kak-tus/compressor/compressor.kicad_pcb

## KiCad design GORAT circuit diagram/GORAT circuit diagram.kicad_pcb

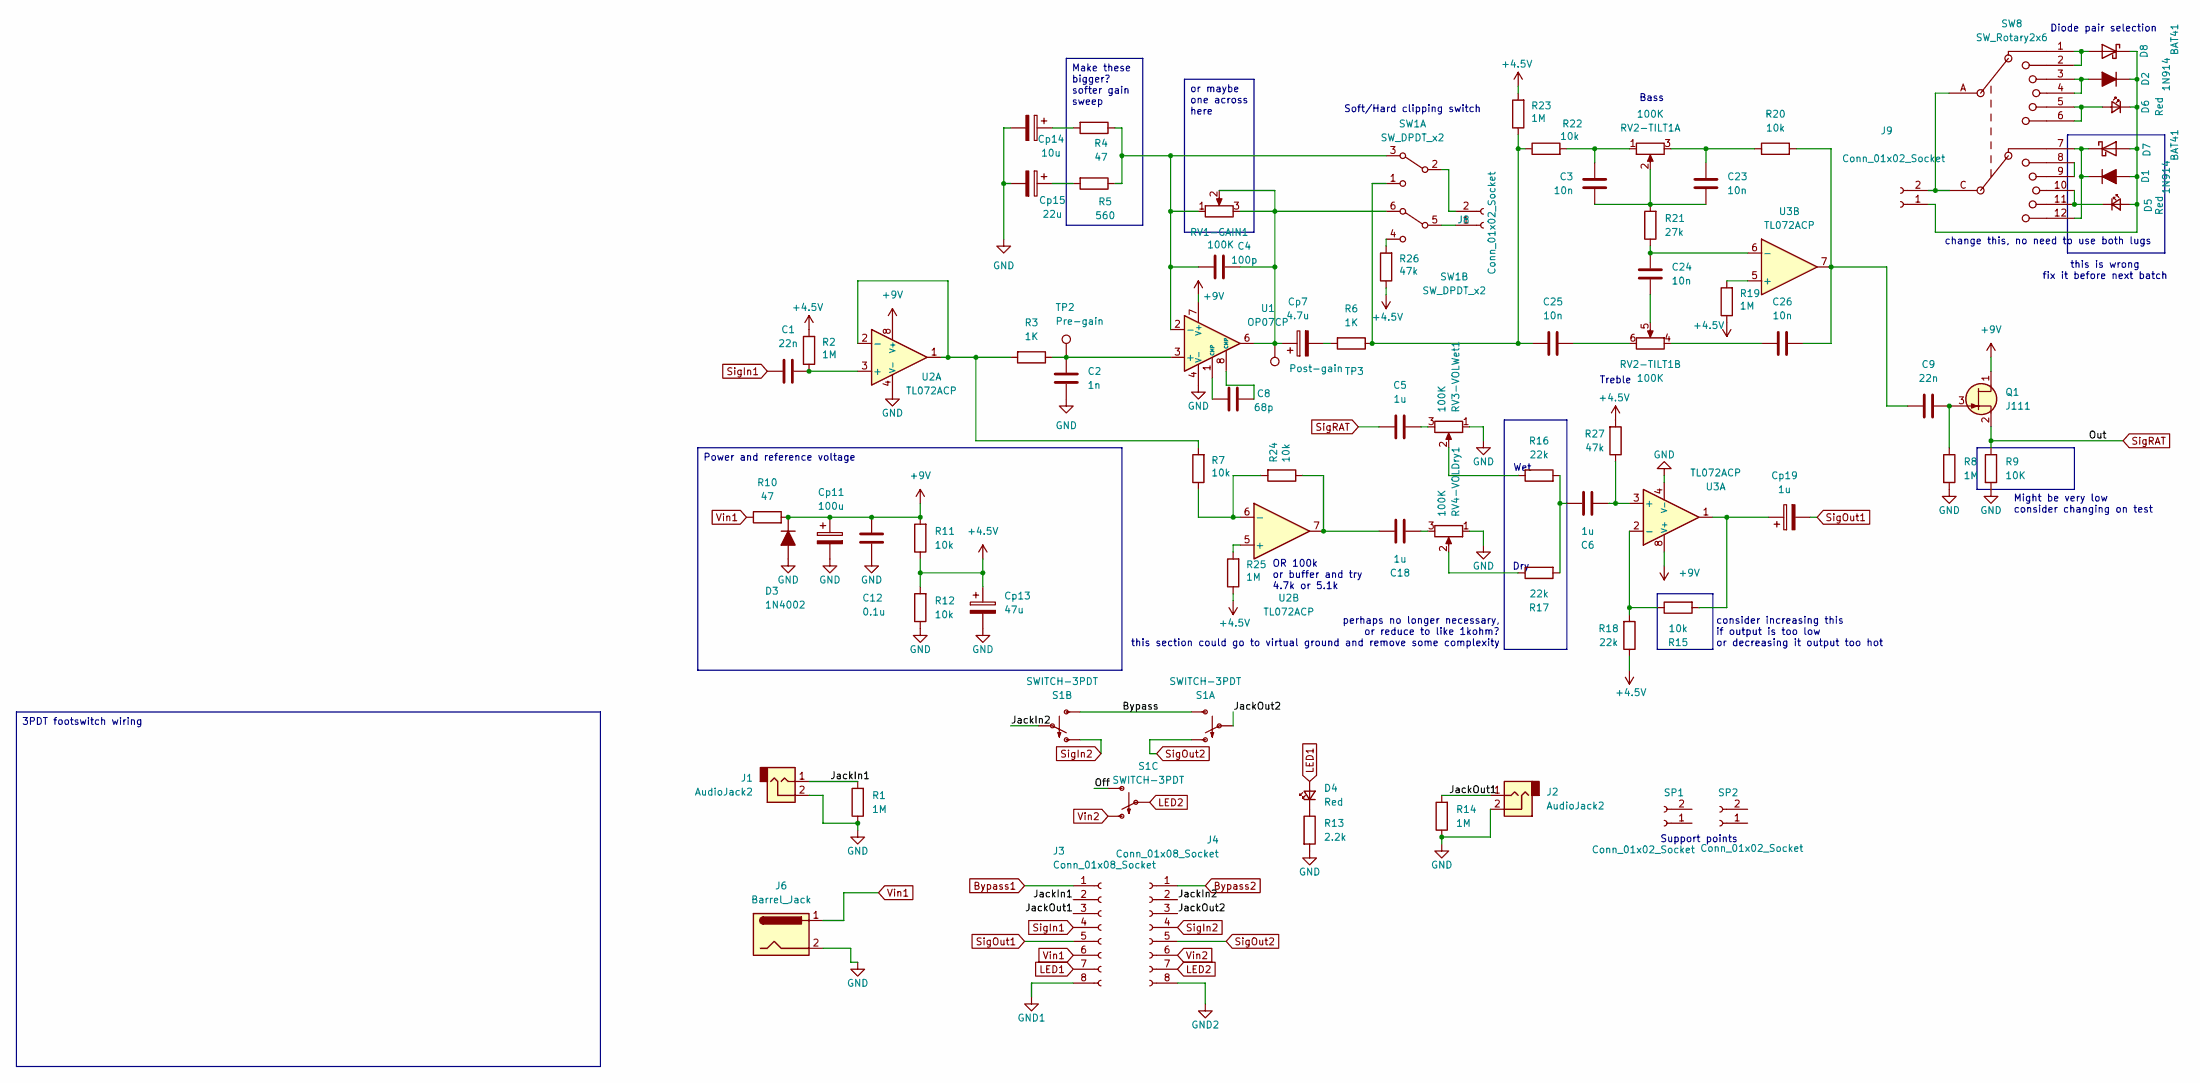
[picture p3: schematic GORAT circuit diagram.kicad_sch]

Parts:
C1, C9: 22n; C_Disc_D4.7mm_W2.5mm_P5.00mm
C2: 1n; C_Disc_D4.7mm_W2.5mm_P5.00mm
C3, C23, C24, C25, C26: 10n; C_Disc_D4.7mm_W2.5mm_P5.00mm
C4: 100p; C_Disc_D4.7mm_W2.5mm_P5.00mm
C5, C6, C18: 1u; C_Disc_D4.7mm_W2.5mm_P5.00mm
C8: 68p; C_Disc_D4.7mm_W2.5mm_P5.00mm
C12: 0.1u; C_Disc_D4.7mm_W2.5mm_P5.00mm
Cp7: 4.7u; CP_Radial_D5.0mm_P2.50mm
Cp11: 100u; CP_Radial_D5.0mm_P2.50mm
Cp13: 47u; CP_Radial_D5.0mm_P2.50mm
Cp14: 10u; CP_Radial_D5.0mm_P2.50mm
Cp15: 22u; CP_Radial_D5.0mm_P2.50mm
Cp19: 1u; CP_Radial_D5.0mm_P2.50mm
D1, D2: 1N914; D_DO-35_SOD27_P7.62mm_Horizontal
D3: 1N4002; D_DO-41_SOD81_P7.62mm_Horizontal
D4: Red; LED_D5.0mm
D5, D6: Red; LED_D3.0mm
D7, D8: BAT41; D_DO-35_SOD27_P7.62mm_Horizontal
J1, J2: AudioJack2; SolderWire-0.75sqmm_1x02_P7mm_D1.25mm_OD3.5mm
J3, J4: Conn_01x08_Socket; PinHeader_1x08_P2.54mm_Vertical
J6: Barrel_Jack; SolderWire-0.5sqmm_1x02_P4.6mm_D0.9mm_OD2.1mm
J8, J9: Conn_01x02_Socket; PinHeader_1x02_P2.54mm_Vertical
Q1: J111; TO-92_Inline_Wide_DSG
R1, R2, R8, R14, R19, R23, R25: 1M; R_Axial_DIN0207_L6.3mm_D2.5mm_P10.16mm_Horizontal
R3, R6: 1K; R_Axial_DIN0207_L6.3mm_D2.5mm_P10.16mm_Horizontal
R4, R10: 47; R_Axial_DIN0207_L6.3mm_D2.5mm_P10.16mm_Horizontal
R5: 560; R_Axial_DIN0207_L6.3mm_D2.5mm_P10.16mm_Horizontal
R7, R11, R12, R15, R20, R22, R24: 10k; R_Axial_DIN0207_L6.3mm_D2.5mm_P10.16mm_Horizontal
R9: 10K; R_Axial_DIN0207_L6.3mm_D2.5mm_P10.16mm_Horizontal
R13: 2.2k; R_Axial_DIN0207_L6.3mm_D2.5mm_P10.16mm_Horizontal
R16, R17, R18: 22k; R_Axial_DIN0207_L6.3mm_D2.5mm_P10.16mm_Horizontal
R21: 27k; R_Axial_DIN0207_L6.3mm_D2.5mm_P10.16mm_Horizontal
R26, R27: 47k; R_Axial_DIN0207_L6.3mm_D2.5mm_P10.16mm_Horizontal
RV1-GAIN1, RV3-VOLWet1, RV4-VOLDry1: 100K; Potentiometer_Alpha_RD901F-40-00D_Single_Vertical
RV2-TILT1: 100K; Potentiometer_Alpha_RD902F-40-00D_Dual_Vertical
S1: SWITCH-3PDT; 3PDT_fixed
SP1, SP2: Conn_01x02_Socket; PinHeader_1x02_P2.54mm_Vertical
SW1: SW_DPDT_x2; DPDT_fixed
SW8: SW_Rotary2x6; RS26
TP2: Pre-gain; TestPoint_Pad_D2.0mm
TP3: Post-gain; TestPoint_Pad_D2.0mm
U1: OP07CP; DIP-8_W7.62mm_LongPads
U2, U3: TL072ACP; DIP-8_W7.62mm_LongPads

Connections:
+4.5V: Cp13.1, R2.2, R11.1, R12.2, R18.1, R19.1, R23.2, R25.1, R26.1, R27.2
+9V: C12.2, Cp11.1, D3.1 (K), Q1.1 (D), R10.2, R11.2, U1.7 (V+), U2.8 (V+), U3.8 (V+)
/Bypass: S1.P$3 (S), S1.P$6 (S)
/JackIn1: J1.1, J3.2, R1.2
/JackIn2: J4.2, S1.P$5
/JackOut1: J2.1, J3.3, R14.2
/JackOut2: J4.3, S1.P$2
/Off: S1.P$9 (S)
Bypass1: J3.1
Bypass2: J4.1
GND: C2.1, C12.1, Cp11.2, Cp13.2, Cp14.2, Cp15.2, D3.2 (A), J1.2, J2.2, J6.2, R1.1, R8.2, R9.2, R12.1, R13.2, R14.1, RV3-VOLWet1.1, RV4-VOLDry1.1, U1.4 (V-), U2.4 (V-), U3.4 (V-)
GND1: J3.8
GND2: J4.8
LED1: D4.2 (A), J3.7
LED2: J4.7, S1.P$8
unnamed: C3.2, R22.2, RV2-TILT1.1
unnamed: C5.2, RV3-VOLWet1.3
unnamed: C6.1, R16.2, R17.2
unnamed: C8.1, U1.1 (CMP)
unnamed: C8.2, U1.8 (CMP)
unnamed: C18.1, R24.1, U2.7
unnamed: C18.2, RV4-VOLDry1.3
unnamed: C3.1, C23.1, R21.2, RV2-TILT1.2
unnamed: C23.2, R20.1, RV2-TILT1.3
unnamed: C24.1, RV2-TILT1.5
unnamed: C25.1, RV2-TILT1.6
unnamed: C9.2, C26.1, R20.2, U3.7
unnamed: C26.2, RV2-TILT1.4
unnamed: Cp7.2, R6.2
unnamed: Cp14.1, R4.2
unnamed: Cp15.1, R5.2
unnamed: Cp19.1, R15.2, U3.1
unnamed: D1.2 (A), D2.1 (K), D5.2 (A), D6.1 (K), D7.2 (A), D8.1 (K), J9.1
unnamed: D1.1 (K), D7.1 (K), SW8.7, SW8.12
unnamed: D2.2 (A), SW8.3, SW8.4
unnamed: D4.1 (K), R13.1
unnamed: D5.1 (K), SW8.10, SW8.11
unnamed: D6.2 (A), SW8.5, SW8.6
unnamed: D8.2 (A), SW8.1, SW8.2
unnamed: J8.1, SW1.5 (B)
unnamed: J8.2, SW1.2 (B)
unnamed: J9.2, SW8.A, SW8.C
unnamed: C9.1, Q1.3 (G), R8.1
unnamed: R16.1, RV3-VOLWet1.2
unnamed: R17.1, RV4-VOLDry1.2
unnamed: C25.2, R6.1, R22.1, R23.1, SW1.1 (A)
unnamed: C4.2, R4.1, R5.1, RV1-GAIN1.1, SW1.3 (C), U1.2 (-)
unnamed: R26.2, SW1.4 (A)
unnamed: C4.1, Cp7.1, RV1-GAIN1.2, RV1-GAIN1.3, SW1.6 (C), TP3.1, U1.6
unnamed: SW8.8, SW8.9
unnamed: C2.2, R3.1, TP2.1, U1.3 (+)
unnamed: C1.2, R2.1, U2.3 (+)
unnamed: R3.2, R7.2, U2.1, U2.2 (-)
unnamed: R25.2, U2.5 (+)
unnamed: R7.1, R24.2, U2.6 (-)
unnamed: C6.2, R27.1, U3.3 (+)
unnamed: R15.1, R18.2, U3.2 (-)
unnamed: R19.2, U3.5 (+)
unnamed: C24.2, R21.1, U3.6 (-)
SigIn1: C1.1, J3.4
SigIn2: J4.4, S1.P$4 (O)
SigOut1: Cp19.2, J3.5
SigOut2: J4.5, S1.P$1 (O)
SigRAT: C5.1, Q1.2 (S), R9.1
Vin1: J3.6, J6.1, R10.1
Vin2: J4.6, S1.P$7 (O)

Notes on the sheet:
Wet
OR 100k or buffer and try 4.7k or 5.1k
Might be very low consider changing on test
Soft/Hard clipping switch
consider increasing this if output is too low or decreasing it output too hot
change this, no need to use both lugs
Treble
Support points
Bass
perhaps no longer necessary, or reduce to like 1kohm? this section could go to virtual ground and remove some complexity
Diode pair selection
Dry
this is wrong fix it before next batch
or maybe one across here
Make these bigger? softer gain sweep
3PDT footswitch wiring
Power and reference voltage

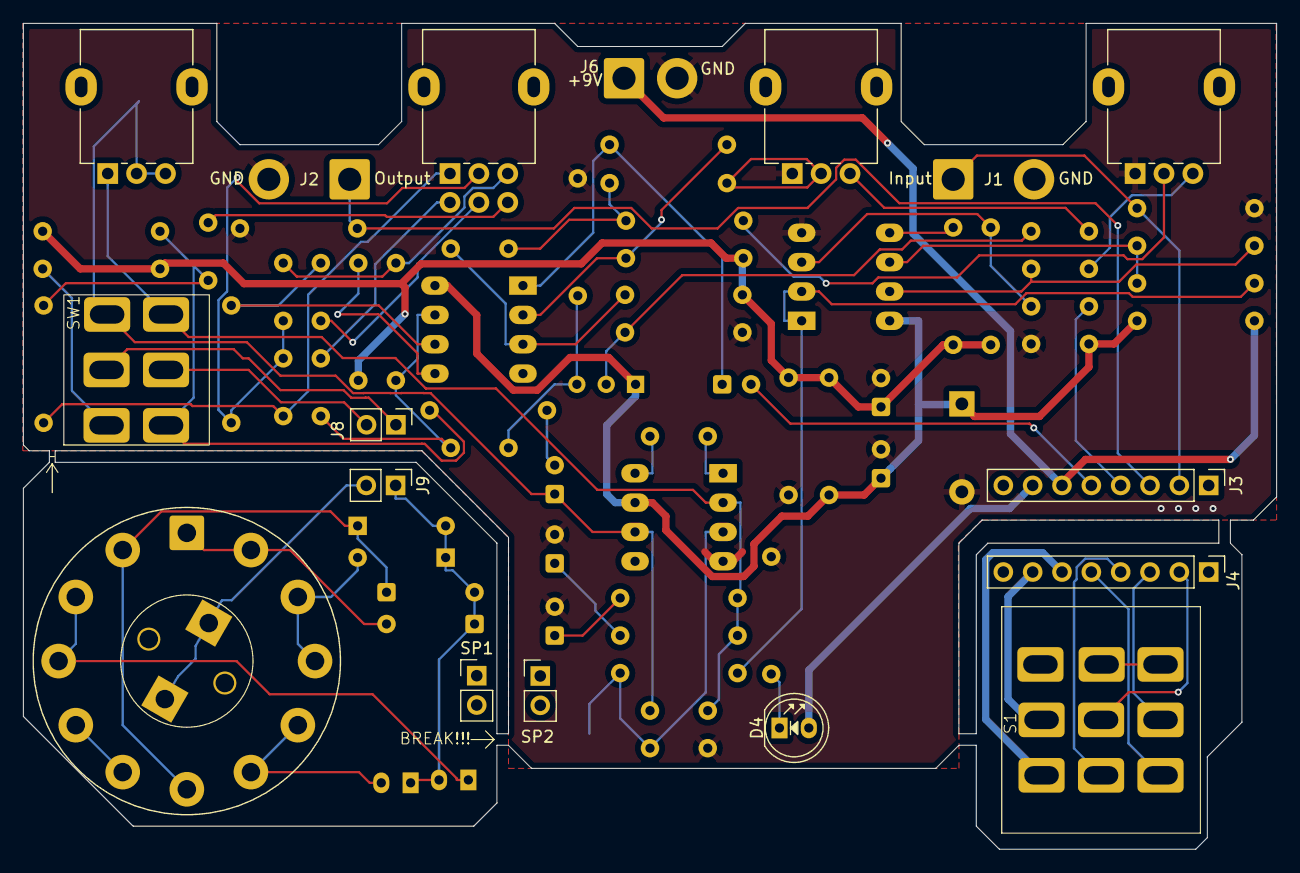
[picture p4: board GORAT circuit diagram.kicad_pcb from above]

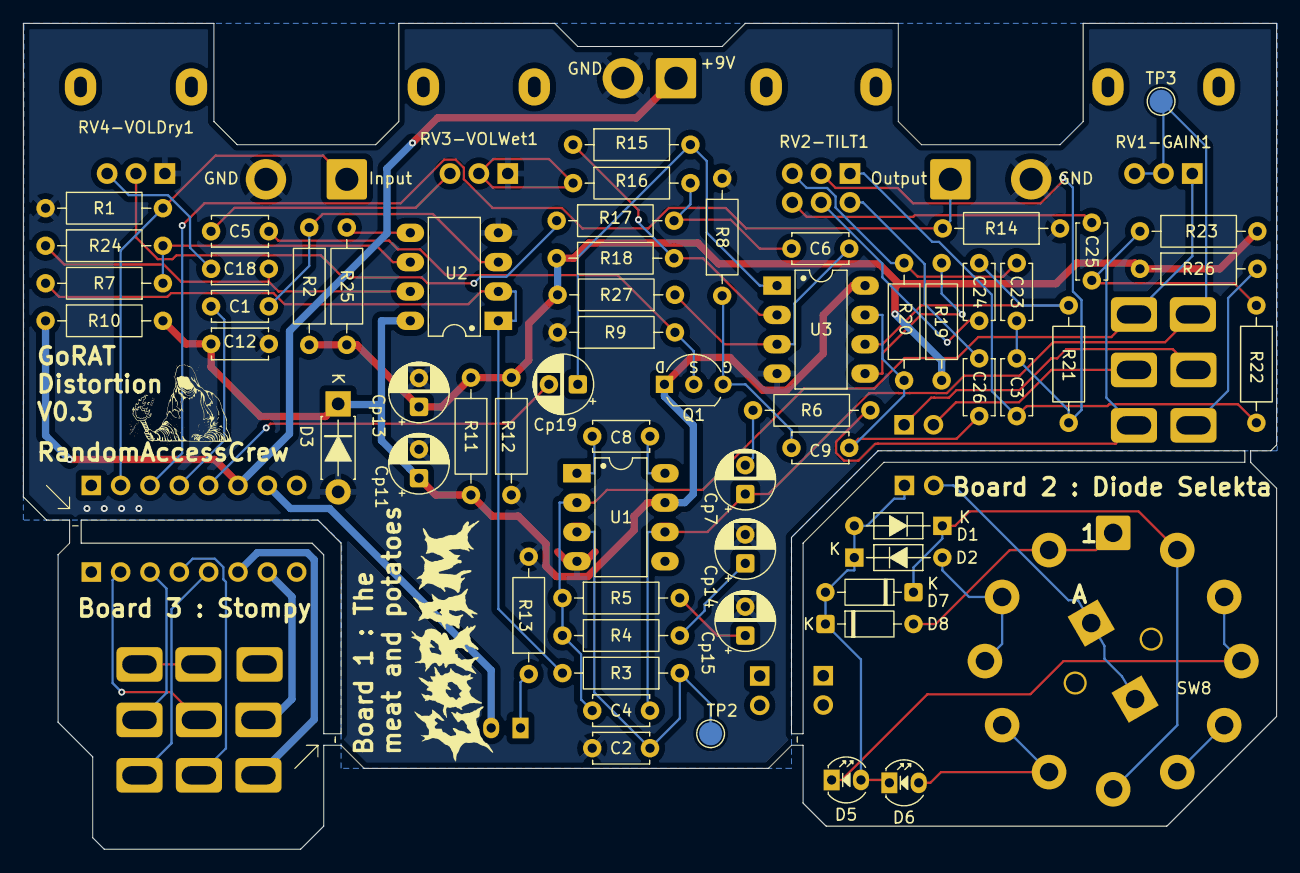
[picture p5: board GORAT circuit diagram.kicad_pcb from below]

Board: 2 copper layers, 108.5 x 71.5 mm, 77 parts (60 on the bottom side), 61 nets.
